AriaMaz/DinoDrive/FinalPresentation/Presentation Photos/Isometric Front View .png

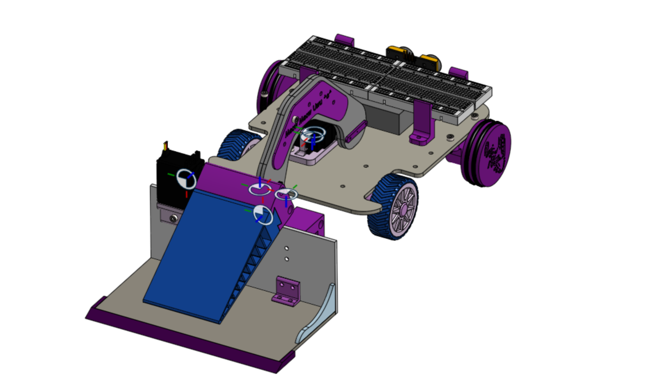
FinalPresentation/Presentation Photos/Isometric Front View .png
