AriaMaz/DinoDrive/FinalPresentation/Presentation Photos/Pic1.png

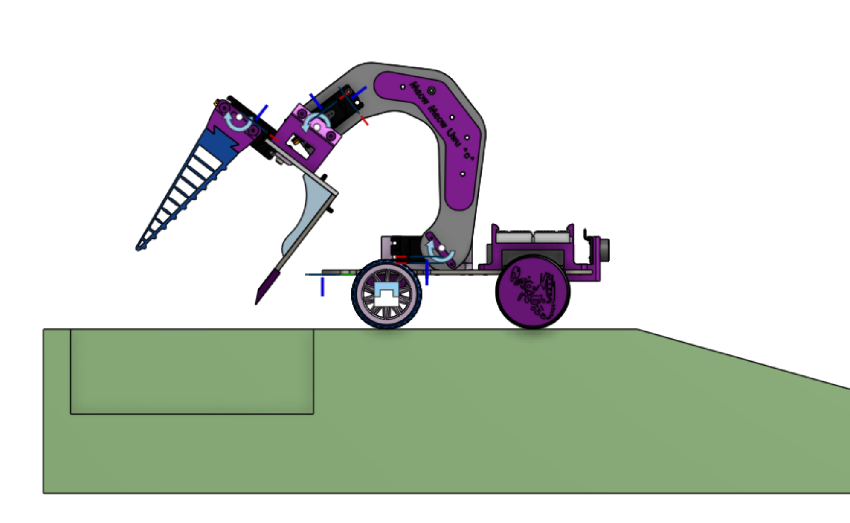
FinalPresentation/Presentation Photos/Pic1.png
