AriaMaz/DinoDrive/FinalPresentation/Presentation Photos/Pic2.png

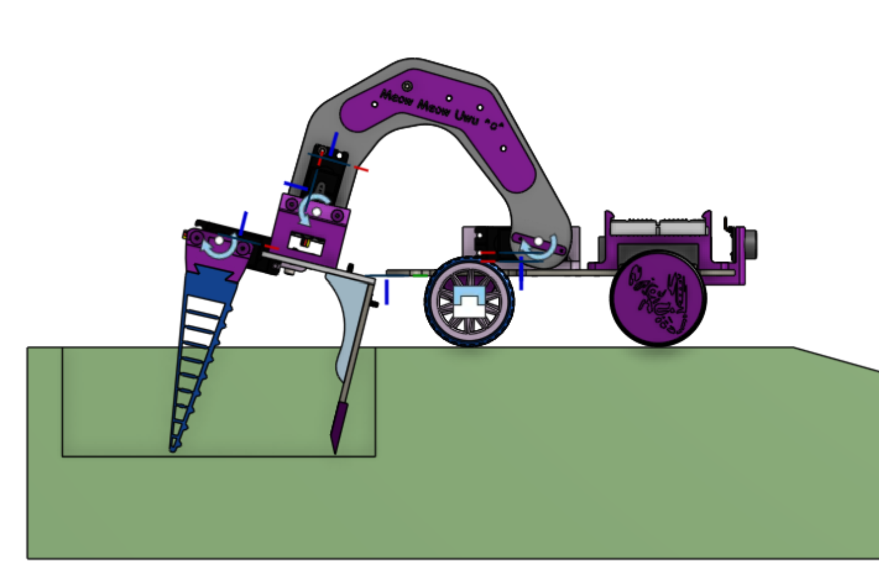
FinalPresentation/Presentation Photos/Pic2.png
