AriaMaz/DinoDrive/FinalPresentation/Presentation Photos/Pic3.png

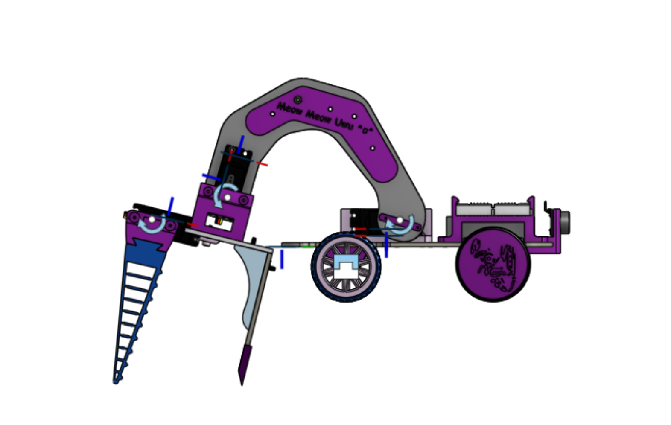
FinalPresentation/Presentation Photos/Pic3.png
