AriaMaz/DinoDrive/FinalPresentation/Presentation Photos/Pic4.png

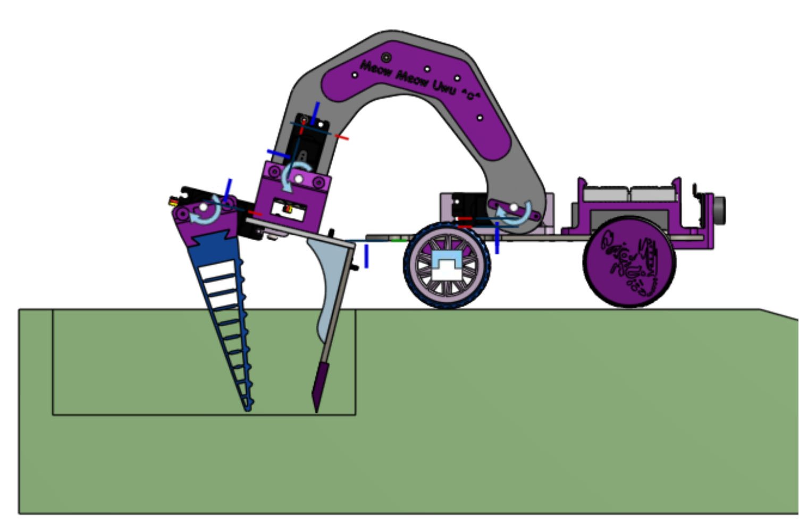
FinalPresentation/Presentation Photos/Pic4.png
