AriaMaz/DinoDrive/FinalPresentation/Presentation Photos/Pic5.png

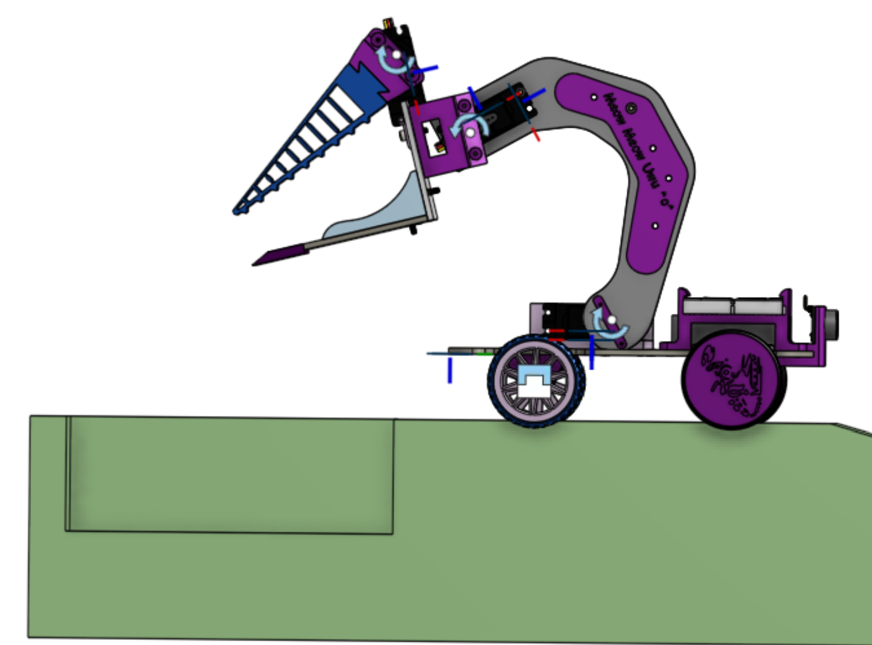
FinalPresentation/Presentation Photos/Pic5.png
