AriaMaz/DinoDrive/FinalPresentation/Presentation Photos/pic6.png

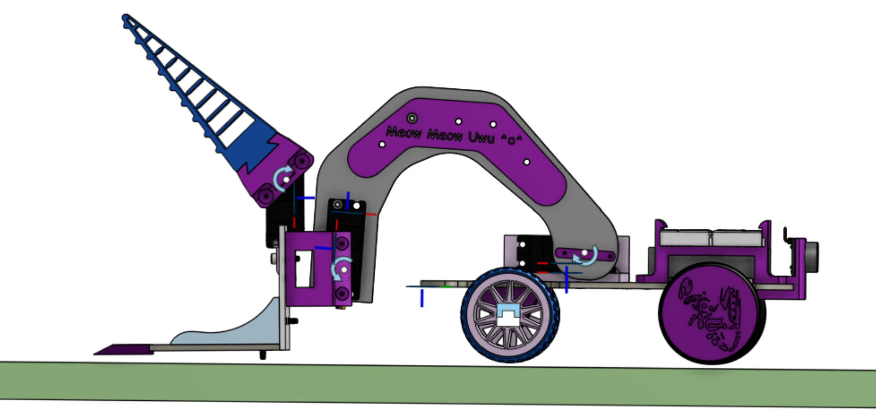
FinalPresentation/Presentation Photos/pic6.png
