AriaMaz/DinoDrive/FinalPresentation/Presentation Photos/Side Profile Crane donw.png

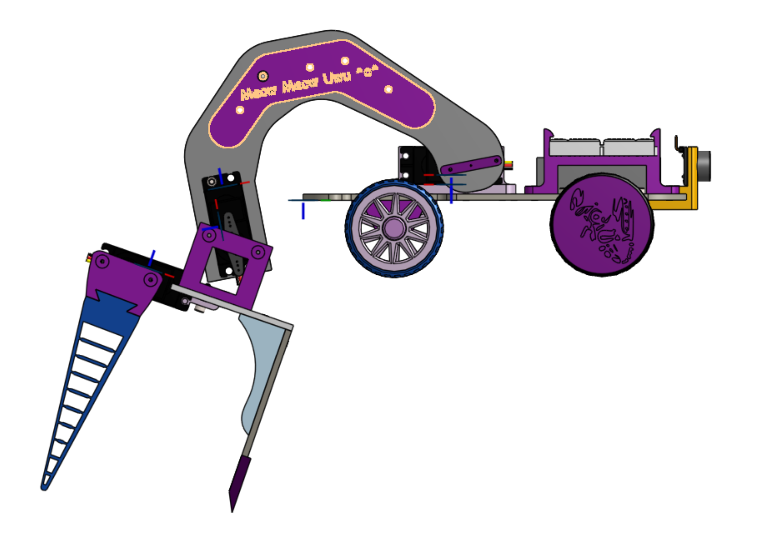
FinalPresentation/Presentation Photos/Side Profile Crane donw.png
