AriaMaz/DinoDrive/FinalPresentation/Presentation Photos/Side Profile Crane up .png

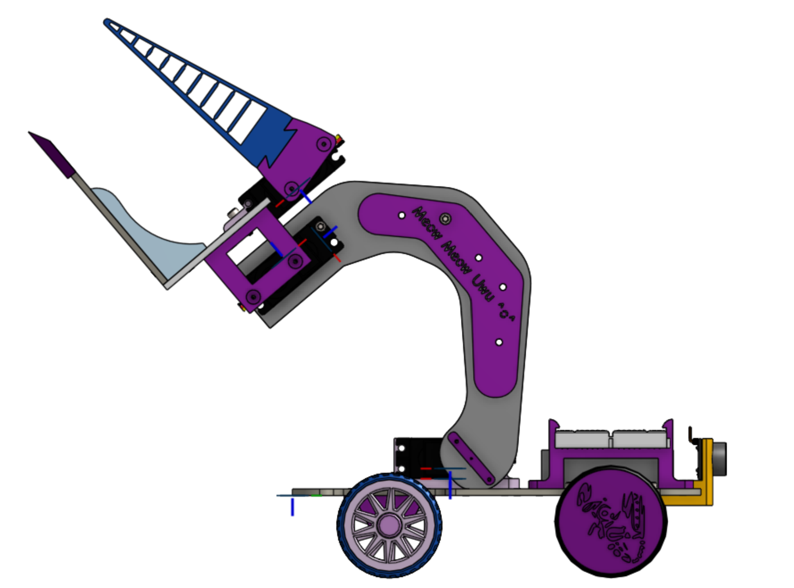
FinalPresentation/Presentation Photos/Side Profile Crane up .png
