AriaMaz/DinoDrive/STL_Files/PLA/Casing + Wheels - Front Wheel Support.stl

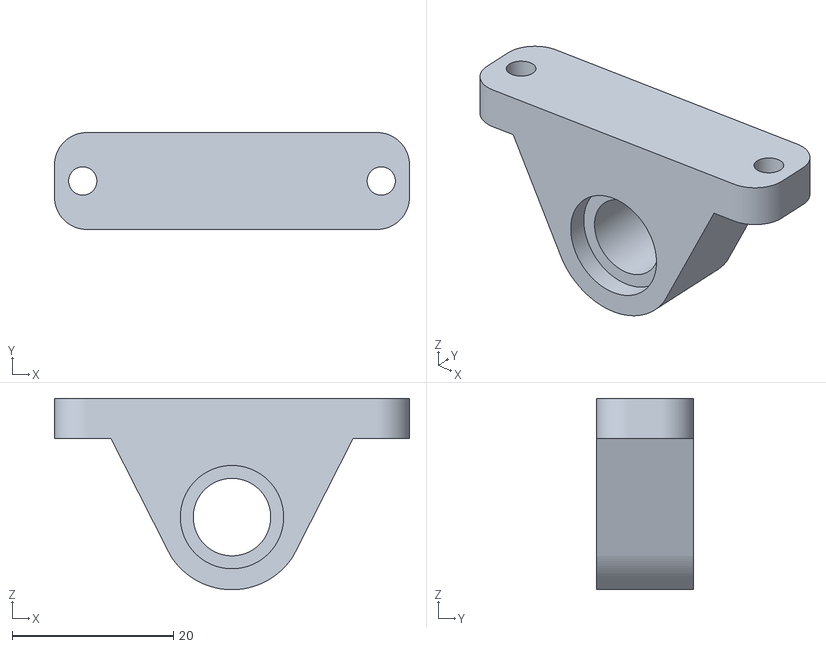
[picture p52: CAD file, 2024-05-19]
STL_Files/PLA/Casing + Wheels - Front Wheel Support.stl
44.0 x 12.0 x 23.7
