AriaMaz/DinoDrive/STL_Files/PLA/Front Wheel Center PLA.stl

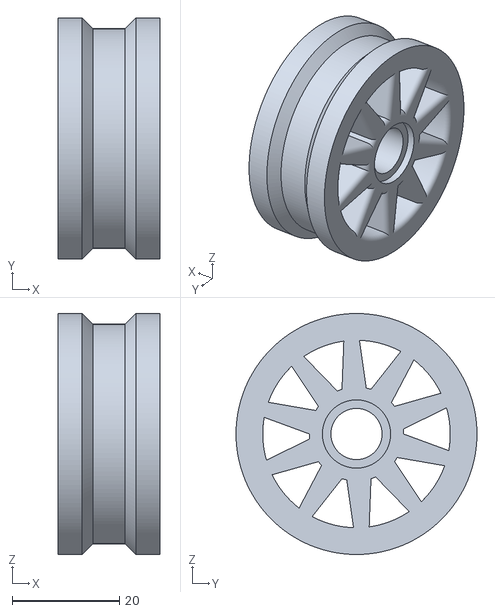
[picture p53: CAD file, 2024-05-19]
STL_Files/PLA/Front Wheel Center PLA.stl
19.0 x 45.0 x 45.0
