AriaMaz/DinoDrive/Round 2/ultrasound_test/ultrasound_test.ino

/* ultrasound_test

   Ultrasonic Sensor HC-SR04 and Raspberry Pi Pico W
  
   Code adapted from Dejan Nedelkovski in www.HowToMechatronics.com
   https://howtomechatronics.com/tutorials/arduino/ultrasonic-sensor-hc-sr04/

*/

// defines pins numbers
const int trigPin = 16;
const int echoPin = 13;

// defines variables
long duration;
int distance;

void setup() {
  pinMode(trigPin, OUTPUT); // Sets the trigPin as an Output
  pinMode(echoPin, INPUT); // Sets the echoPin as an Input
  Serial.begin(9600); // Starts the serial communication
}

void loop() {
  // Clears the trigPin
  digitalWrite(trigPin, LOW);
  delayMicroseconds(2);

  // Sets the trigPin on HIGH state for 10 micro seconds
  digitalWrite(trigPin, HIGH);
  delayMicroseconds(10);
  digitalWrite(trigPin, LOW);
  
  // Reads the echoPin, returns the sound wave travel time in microseconds
  duration = pulseIn(echoPin, HIGH);
  Serial.print(duration);

  // Calculating the distance
  distance = duration * 0.034 / 2;

  // Prints the distance on the Serial Monitor
  Serial.print("Distance (cm): ");
  Serial.println(distance);
  delay(100);

}
